automaticdai/arduino-yaoji/photos/RGB调色2.jpg

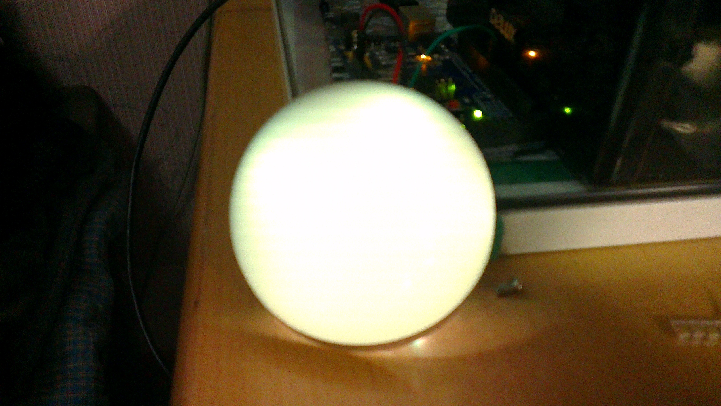
photos/RGB调色2.jpg
